Joost2S/kas-control/Code/kascontrol/electronics/drivers/hd44780.py

#!/usr/bin/python3
# Copied from: https://github.com/adafruit/Adafruit_Python_CharLCD
# v 21 Sep 2017
# Copyright (c) 2014 Adafruit Industries
# Author: Tony DiCola
#
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
import RPi.GPIO as GPIO


# Commands
LCD_CLEARDISPLAY        = 0x01
LCD_RETURNHOME          = 0x02
LCD_ENTRYMODESET        = 0x04
LCD_DISPLAYCONTROL      = 0x08
LCD_CURSORSHIFT         = 0x10
LCD_FUNCTIONSET         = 0x20
LCD_SETCGRAMADDR        = 0x40
LCD_SETDDRAMADDR        = 0x80

# Entry flags
LCD_ENTRYRIGHT          = 0x00
LCD_ENTRYLEFT           = 0x02
LCD_ENTRYSHIFTINCREMENT = 0x01
LCD_ENTRYSHIFTDECREMENT = 0x00

# Control flags
LCD_DISPLAYON           = 0x04
LCD_DISPLAYOFF          = 0x00
LCD_CURSORON            = 0x02
LCD_CURSOROFF           = 0x00
LCD_BLINKON             = 0x01
LCD_BLINKOFF            = 0x00

# Move flags
LCD_DISPLAYMOVE         = 0x08
LCD_CURSORMOVE          = 0x00
LCD_MOVERIGHT           = 0x04
LCD_MOVELEFT            = 0x00

# Function set flags
LCD_8BITMODE            = 0x10
LCD_4BITMODE            = 0x00
LCD_2LINE               = 0x08
LCD_1LINE               = 0x00
LCD_5x10DOTS            = 0x04
LCD_5x8DOTS             = 0x00

# Offset for up to 4 rows.
LCD_ROW_OFFSETS         = (0x00, 0x40, 0x14, 0x54)


class Adafruit_CharLCD(object):
	"""Class to represent and interact with an HD44780 character LCD display."""

	def __init__(self, pins, cols, lines, invert_polarity = True,
	             gpio = GPIO, initial_backlight = 1.0):

		"""Initialize the LCD.  RS, EN, and D4...D7 parameters should be the pins
		connected to the LCD RS, clock enable, and data line 4 through 7 connections.
		The LCD will be used in its 4-bit mode so these 6 lines are the only ones
		required to use the LCD.  You must also pass in the number of columns and
		lines on the LCD.

		If you would like to control the backlight, pass in the pin connected to
		the backlight with the backlight parameter.  The invert_polarity boolean
		controls if the backlight is one with a LOW signal or HIGH signal.  The
		default invert_polarity value is True, i.e. the backlight is on with a
		LOW signal.

		You can enable PWM of the backlight pin to have finer control on the
		brightness.  To enable PWM make sure your hardware supports PWM on the
		provided backlight pin and set enable_pwm to True (the default is False).
		The appropriate PWM library will be used depending on the platform, but
		you can provide an explicit one with the pwm parameter.

		The initial state of the backlight is ON, but you can set it to an
		explicit initial state with the initial_backlight parameter (0 is off,
		1 is on/full bright).

		You can optionally pass in an explicit GPIO class,
		for example if you want to use an MCP230xx GPIO extender.  If you don't
		pass in a GPIO instance, the default GPIO for the running platform will
		be used.
		"""
		# Save column and line state.
		self._cols = cols
		self._lines = lines
		# Save GPIO state and pin numbers.
		self._gpio = gpio
		self._rs = pins["LCD_RS"]
		self._en = pins["LCD_E"]
		self._d4 = pins["LCD4"]
		self._d5 = pins["LCD5"]
		self._d6 = pins["LCD6"]
		self._d7 = pins["LCD7"]
		# Save backlight state.
		self._backlight = pins["LCD_L"]
		# self._pwm_enabled = enable_pwm
		# self._pwm = pwm
		self._blpol = not invert_polarity
		# Setup all pins as outputs.
		for pin in (pins.values()):
			gpio.setup(pin, GPIO.OUT)
		# Setup backlight.
		if self._backlight is not None:
			gpio.setup(self._backlight, GPIO.OUT)
			gpio.output(self._backlight, self._blpol if initial_backlight else not self._blpol)
		# Initialize the display.
		self.write8(0x33)
		self.write8(0x32)
		# Initialize display control, function, and mode registers.
		self.displaycontrol = LCD_DISPLAYON | LCD_CURSOROFF | LCD_BLINKOFF
		self.displayfunction = LCD_4BITMODE | LCD_1LINE | LCD_2LINE | LCD_5x8DOTS
		self.displaymode = LCD_ENTRYLEFT | LCD_ENTRYSHIFTDECREMENT
		# Write registers.
		self.write8(LCD_DISPLAYCONTROL | self.displaycontrol)
		self.write8(LCD_FUNCTIONSET | self.displayfunction)
		self.write8(LCD_ENTRYMODESET | self.displaymode)  # set the entry mode
		self.clear()

	def home(self):
		"""Move the cursor back to its home (first line and first column)."""
		self.write8(LCD_RETURNHOME)  # set cursor position to zero
		self._delay_microseconds(3000)  # this command takes a long time!

	def clear(self):
		"""Clear the LCD."""
		self.write8(LCD_CLEARDISPLAY)  # command to clear display
		self._delay_microseconds(3000)  # 3000 microsecond sleep, clearing the display takes a long time

	def set_cursor(self, col, row):
		"""Move the cursor to an explicit column and row position."""
		# Clamp row to the last row of the display.
		if row > self._lines:
			row = self._lines - 1
		# Set location.
		self.write8(LCD_SETDDRAMADDR | (col + LCD_ROW_OFFSETS[row]))

	def enable_display(self, enable):
		"""Enable or disable the display.  Set enable to True to enable."""
		if enable:
			self.displaycontrol |= LCD_DISPLAYON
		else:
			self.displaycontrol &= ~LCD_DISPLAYON
			self.set_backlight(0)
		self.write8(LCD_DISPLAYCONTROL | self.displaycontrol)

	def show_cursor(self, show):
		"""Show or hide the cursor.  Cursor is shown if show is True."""
		if show:
			self.displaycontrol |= LCD_CURSORON
		else:
			self.displaycontrol &= ~LCD_CURSORON
		self.write8(LCD_DISPLAYCONTROL | self.displaycontrol)

	def blink(self, blink):
		"""Turn on or off cursor blinking.  Set blink to True to enable blinking."""
		if blink:
			self.displaycontrol |= LCD_BLINKON
		else:
			self.displaycontrol &= ~LCD_BLINKON
		self.write8(LCD_DISPLAYCONTROL | self.displaycontrol)

	def move_left(self):
		"""Move display left one position."""
		self.write8(LCD_CURSORSHIFT | LCD_DISPLAYMOVE | LCD_MOVELEFT)

	def move_right(self):
		"""Move display right one position."""
		self.write8(LCD_CURSORSHIFT | LCD_DISPLAYMOVE | LCD_MOVERIGHT)

	def set_left_to_right(self):
		"""Set text direction left to right."""
		self.displaymode |= LCD_ENTRYLEFT
		self.write8(LCD_ENTRYMODESET | self.displaymode)

	def set_right_to_left(self):
		"""Set text direction right to left."""
		self.displaymode &= ~LCD_ENTRYLEFT
		self.write8(LCD_ENTRYMODESET | self.displaymode)

	def autoscroll(self, autoscroll):
		"""Autoscroll will 'right justify' text from the cursor if set True,
		otherwise it will 'left justify' the text.
		"""
		if autoscroll:
			self.displaymode |= LCD_ENTRYSHIFTINCREMENT
		else:
			self.displaymode &= ~LCD_ENTRYSHIFTINCREMENT
		self.write8(LCD_ENTRYMODESET | self.displaymode)

	def message(self, text):
		"""Write text to display.  Note that text can include newlines."""
		line = 0
		# Iterate through each character.
		for char in text:
			# Advance to next line if character is a new line.
			if char == '\n':
					line += 1
					# Move to left or right side depending on text direction.
					col = 0 if self.displaymode & LCD_ENTRYLEFT > 0 else self._cols-1
					self.set_cursor(col, line)
			# Write the character to the display.
			else:
					self.write8(ord(char), True)

	def set_backlight(self, backlight):
		"""Enable or disable the backlight.  If PWM is not enabled (default), a
		non-zero backlight value will turn on the backlight and a zero value will
		turn it off.  If PWM is enabled, backlight can be any value from 0.0 to
		1.0, with 1.0 being full intensity backlight.
		"""
		if self._backlight is not None:
				self._gpio.output(self._backlight, self._blpol if backlight else not self._blpol)

	def write8(self, value, char_mode=False):
		"""Write 8-bit value in character or data mode.  Value should be an int
		value from 0-255, and char_mode is True if character data or False if
		non-character data (default).
		"""
		# One millisecond delay to prevent writing too quickly.
		self._delay_microseconds(1000)
		# Set character / data bit.
		self._gpio.output(self._rs, char_mode)
		# Write upper 4 bits.
		for i, pin in enumerate([self._d4, self._d5, self._d6, self._d7]):
			self._gpio.output(pin, ((value >> i + 4) & 1) > 0)
#										self._d5: ((value >> 5) & 1) > 0,
#										self._d6: ((value >> 6) & 1) > 0,
#										self._d7: ((value >> 7) & 1) > 0 })
		self._pulse_enable()
		# Write lower 4 bits.
		for i, pin in enumerate([self._d4, self._d5, self._d6, self._d7]):
			self._gpio.output(pin, ((value >> i) & 1) > 0)
#		self._gpio.output({ self._d4: (value        & 1) > 0,
#										self._d5: ((value >> 1) & 1) > 0,
#										self._d6: ((value >> 2) & 1) > 0,
#										self._d7: ((value >> 3) & 1) > 0 })
		self._pulse_enable()

	def create_char(self, location, pattern):
		"""Fill one of the first 8 CGRAM locations with custom characters.
		The location parameter should be between 0 and 7 and pattern should
		provide an array of 8 bytes containing the pattern. E.g. you can easyly
		design your custom character at http://www.quinapalus.com/hd44780udg.html
		To show your custom character use eg. lcd.message('\x01')
		"""
		# only position 0..7 are allowed
		location &= 0x7
		self.write8(LCD_SETCGRAMADDR | (location << 3))
		for i in range(8):
			self.write8(pattern[i], char_mode=True)

	def _delay_microseconds(self, microseconds):
		# Busy wait in loop because delays are generally very short (few microseconds).
		end = time.time() + (microseconds/1000000.0)
		while time.time() < end:
			pass

	def _pulse_enable(self):
		# Pulse the clock enable line off, on, off to send command.
		self._gpio.output(self._en, False)
		self._delay_microseconds(1)       # 1 microsecond pause - enable pulse must be > 450ns
		self._gpio.output(self._en, True)
		self._delay_microseconds(1)       # 1 microsecond pause - enable pulse must be > 450ns
		self._gpio.output(self._en, False)
		self._delay_microseconds(1)       # commands need > 37us to settle
