Joost2S/kas-control/Code/kascontrol/electronics/managers/adcmanager.py

#!/usr/bin/python3

# Author: J. Saarloos
# v0.01.05	24-05-2019

"""
Manages all ADC pins on supported devices.
Upon setting a pin a UUID is returned by which it is easy to get the
data that is required through the read() method. It is also still
possible to get the data by the readPin() method. This reqires the
address, chip number or board designation of the ADC chip along with
the channel.
Flip-flop pins will be set here and the uuid will be passed to the
appropriaate IC.
"""


import logging
import uuid

from Code.kascontrol.electronics.drivers.mcp3x0x import MCP3004
from Code.kascontrol.electronics.drivers.mcp3x0x import MCP3008
from Code.kascontrol.electronics.drivers.mcp3x0x import MCP3204
from Code.kascontrol.electronics.drivers.mcp3x0x import MCP3208
from Code.kascontrol.globstuff import globstuff as gs
from Code.kascontrol.utils.errors import AbortInitError, ADCconfigError
from Code.kascontrol.utils.threadingutils import TimeoutLock


class ADCmanager(object):

	__adclock = None
	devByAddr = dict()
	devByBoardDes = dict()
	devByNr = dict()
	devSetups = list()
	finalized = False
	__setPins = list() # pins that are set up are registered here so no duplicates are set.
					# gets deleted upon finalisation of manager
	pinList = dict() # list of all set pins. Used throughout program lifecycle.

	def __init__(self, gpio, spi, timeout):
		super(ADCmanager, self).__init__()

		self.__adclock = TimeoutLock(timeout).acquire_timeout
		self.devices = dict()
		self.gpio = gpio
		self.spi = spi
		self.supportedDevices = {
			"mcp3004": MCP3004,
			"mcp3008": MCP3008,
			"mcp3204": MCP3204,
			"mcp3208": MCP3208
		}
		self.setDevices()

	def setDevices(self):

		data = gs.getSetupFile("hardware")["adc"]
		for adcType, devs in data.items():
			for setup in devs:
				try:
					uid = uuid.uuid4()
					spi = self.spi.registerDevice(setup["spiChannel"])
					if spi is False:
						logging.critical("Failed to register spi channel for ADC {}.".format(setup["boardDesignation"]))
						continue
					dev = self.supportedDevices[adcType](
						spi=spi,
						dev=self.spi,
						tlock=self.__adclock,
						gpio=self.gpio
					)
					self.__setDevChannels(dev, setup["channels"], setup["boardDesignation"])
					self.devices[uid] = dev
					self.devByAddr[setup["spiChannel"]] = dev
					self.devByBoardDes[setup["boardDesignation"]] = dev
					self.devByNr[setup["number"]] = dev
				except KeyError:
					continue
				except ADCconfigError:
					raise AbortInitError

	def __setDevChannels(self, dev, channels, devDes):

		if len(channels) != dev.chanAmount:
			logging.critical("Incorrent amount of channels defined for ADC device {}.".format(devDes))
			raise ADCconfigError
		for i, setup in enumerate(channels):
			if not setup["flip-flop"]:
				dev.setChannel(i, i)
			else:
				try:
					p1 = setup["pins"][0]
					p2 = setup["pins"][1]
				except KeyError:
					logging.critical("Too few flip-flop pins have been defined for channel {} on ADC {}.".format(i, devDes))
					raise ADCconfigError
				try:
					ff1 = self.gpio.setPin(p1["pin"], False, devNr=p1["devNumber"])
					ff2 = self.gpio.setPin(p2["pin"], False, devNr=p2["devNumber"])
				except KeyError:
					logging.critical("Flip-flop pins were incorrectly configured for channel {} on ADC {}.".format(i, devDes))
					raise ADCconfigError
				dev.setChannel(i, i, ff1, ff2)

	def setChannel(self, channel, devAddr=None, devNr=None, devDes=None):

		check, dev = self.getDevice(devAddr, devNr, devDes)
		if check is False:
			logging.warning("Tried to set a channel on unknown ADC device: {}".format(dev))
			return False
		if 0 > channel >= dev.chanAmount:
			return False
		pin = {"dev": dev,
            "chan": channel}
		if pin in self.pinList.values():
			logging.warning("ADC {} channel {} already in use.".format(dev.spiChan, channel))
			return False

		uid = uuid.uuid4()
		self.pinList[uid] = pin
		return uid

	def read(self, pin, perc=None):

		try:
			channel = self.pinList[pin]
			return channel["dev"].getMeasurement(channel["chan"], perc=perc)
		except KeyError:
			return None

	def readPin(self, pin, devAddr=None, devNr=None, devDes=None, perc=False):
		check, dev = self.getDevice(devAddr, devNr, devDes)
		if not check:
			return None
		try:
			return dev.getMeasurement(pin, perc=perc)
		except KeyError:
			return None

	def getResolution(self, pin=None, devAddr=None, devNr=None, devDes=None):

		if pin is not None:
			try:
				return self.pinList[pin]["dev"].getResolution()
			except KeyError:
				return None
		check, dev = self.getDevice(devAddr, devNr, devDes)
		if not check:
			return None
		return dev.getResolution()

	def setLockTimeout(self, t):

		self.__adclock.timeout = 0.5 * t

	def getDevice(self, devAddr=None, devNr=None, devDes=None):

		if devAddr is not None:
			try:
				return self.devByAddr[devAddr]
			except KeyError:
				return False, devAddr

		if devNr is not None:
			try:
				return self.devByNr[devNr]
			except KeyError:
				return False, devNr

		if devDes is not None:
			try:
				return self.devByBoardDes[devDes]
			except KeyError:
				return False, devDes

		return False, None
